Pyro57000/fyer_deck/images/20250414_184634.jpg

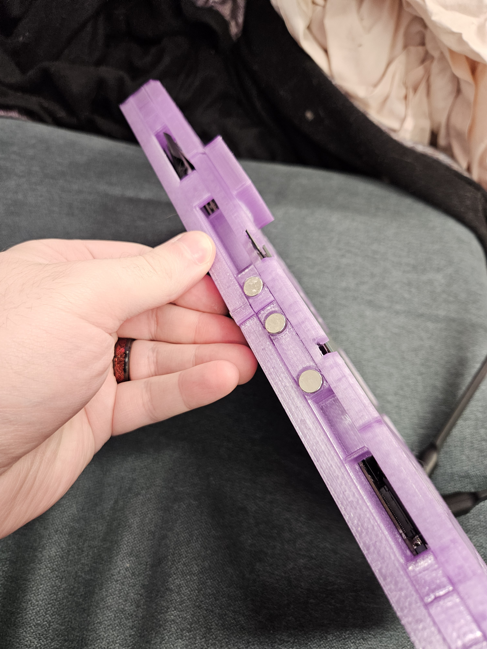
images/20250414_184634.jpg
