Pyro57000/fyer_deck/stls/fyerdeck_files/connect_pin.stl

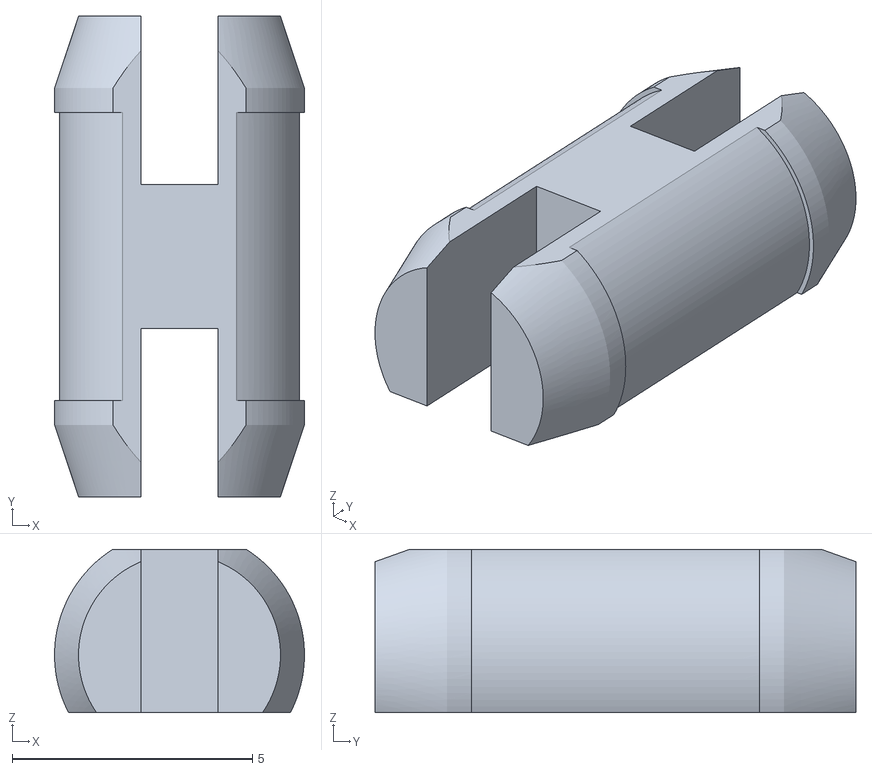
[picture p21: CAD file, 2025-03-23]
stls/fyerdeck_files/connect_pin.stl
5.20 x 10.0 x 3.40
