Pyro57000/fyer_deck/images/20250515_104900.jpg

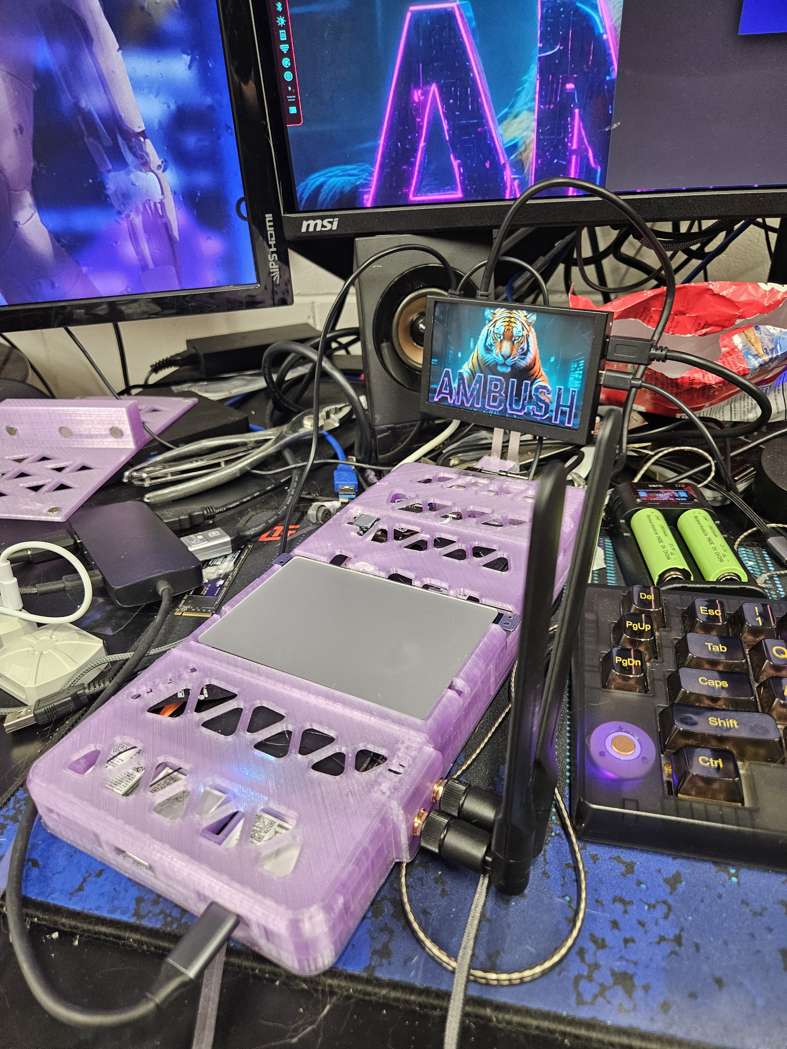
images/20250515_104900.jpg
